ttempe/Pocket_Organ/3D models/V11 mock-up/Rendering with cover plate, flat surface.PNG

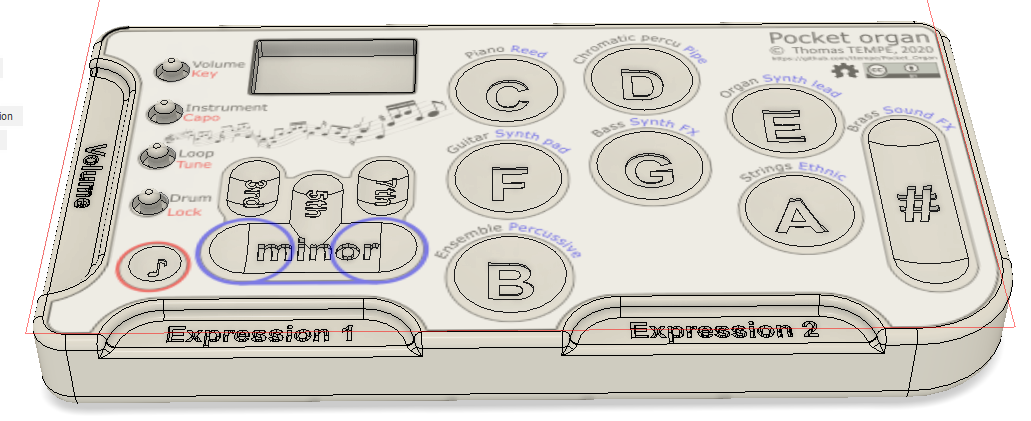
3D models/V11 mock-up/Rendering with cover plate, flat surface.PNG
