ttempe/Pocket_Organ/3D models/V11 mock-up/Rendering without cover plate.PNG

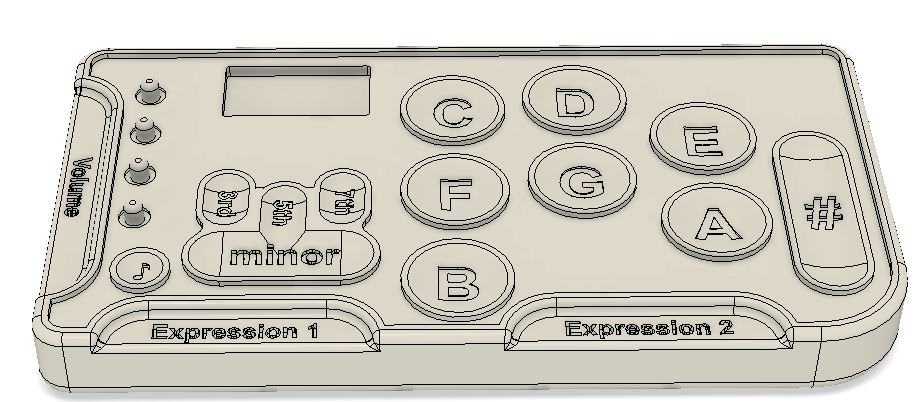
3D models/V11 mock-up/Rendering without cover plate.PNG
