ttempe/Pocket_Organ/Doc/2021-08-28 V19B/微信图片_20210825201405.jpg

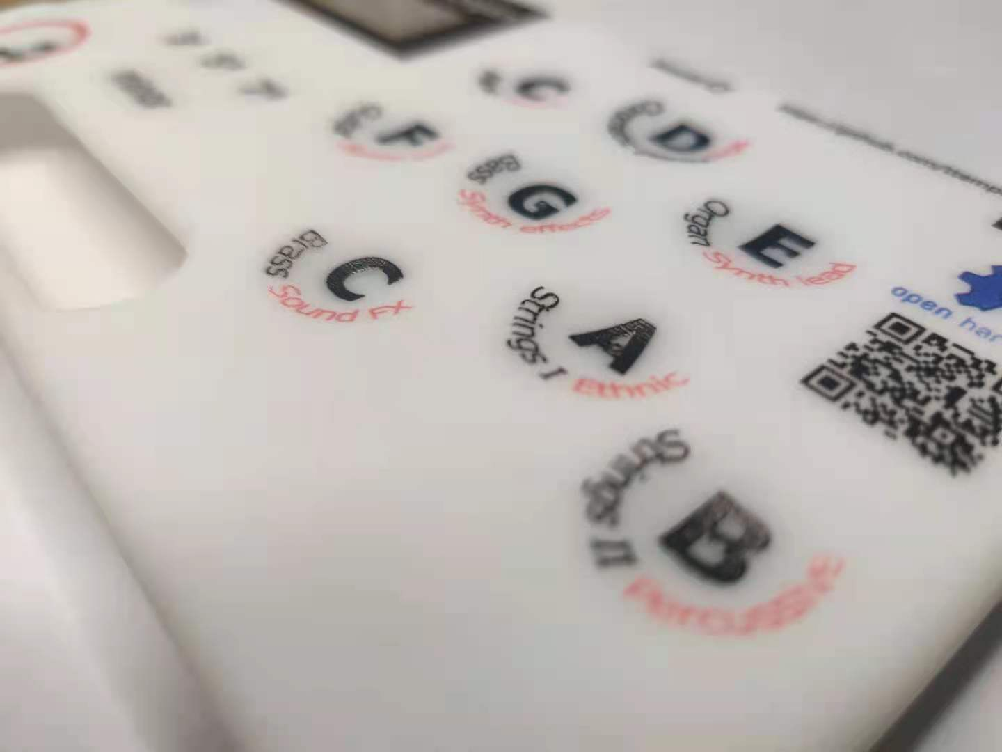
Doc/2021-08-28 V19B/微信图片_20210825201405.jpg
