ttempe/Pocket_Organ/Doc/2021-08-28 V19B/微信图片_20210828121017.jpg

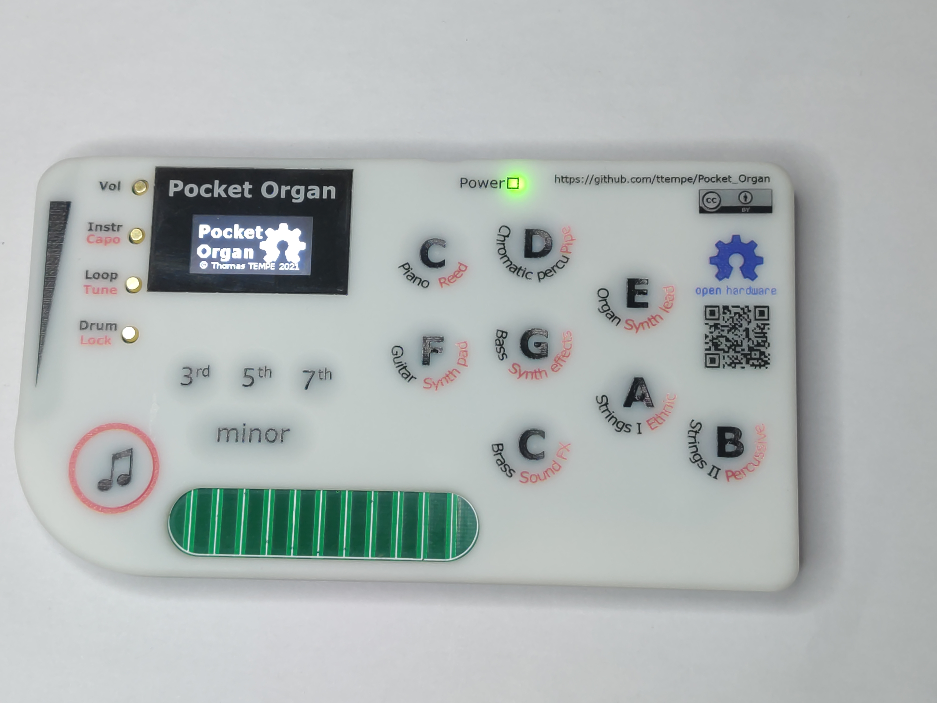
Doc/2021-08-28 V19B/微信图片_20210828121017.jpg
