ttempe/Pocket_Organ/Pictures/V3+/IMG_20180710_225816.jpg

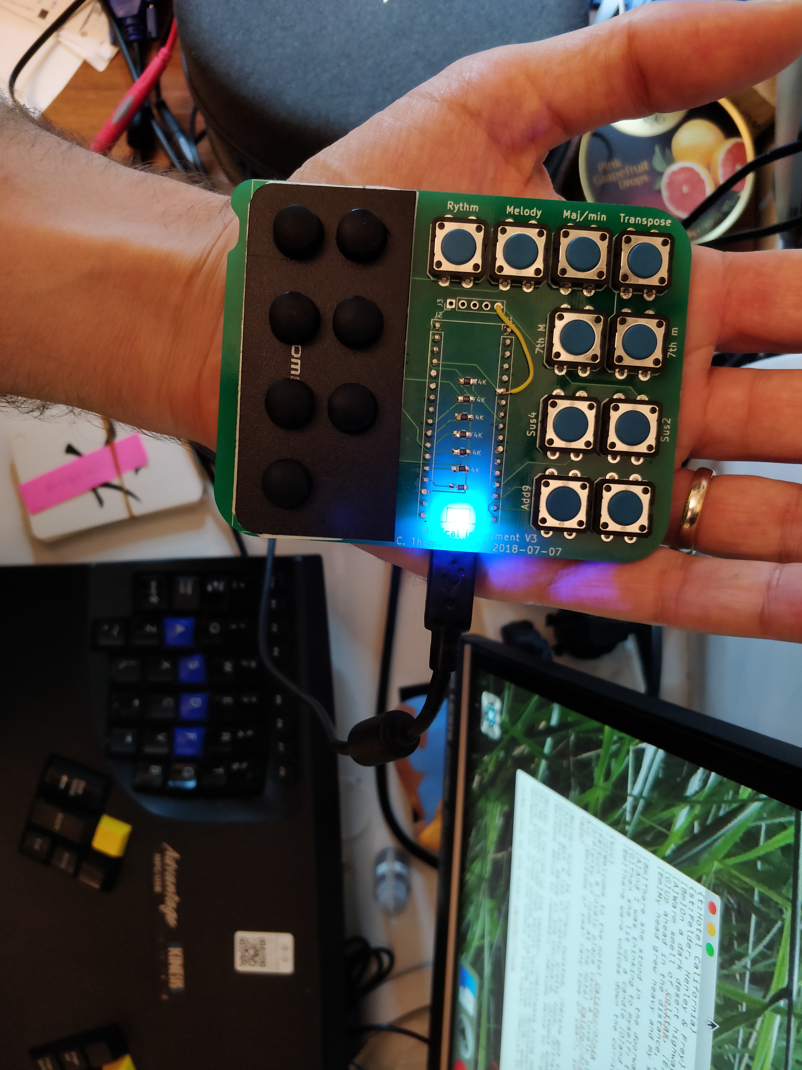
Pictures/V3+/IMG_20180710_225816.jpg
