ttempe/Pocket_Organ/Pictures/V3+/IMG_20190224_225914.jpg

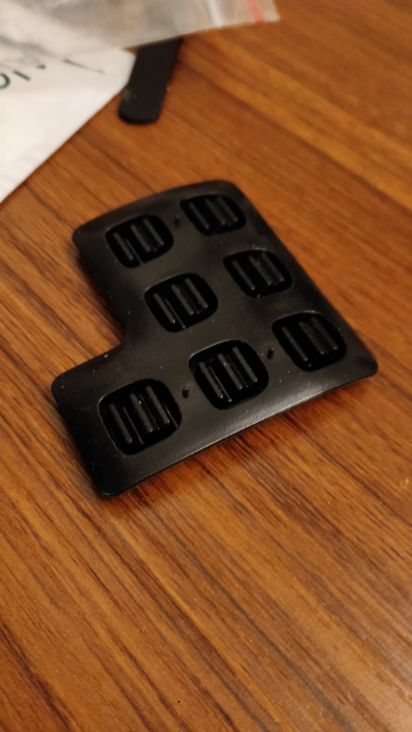
Pictures/V3+/IMG_20190224_225914.jpg
