ttempe/Pocket_Organ/Pictures/V3+/微信图片_20190317143241.jpg

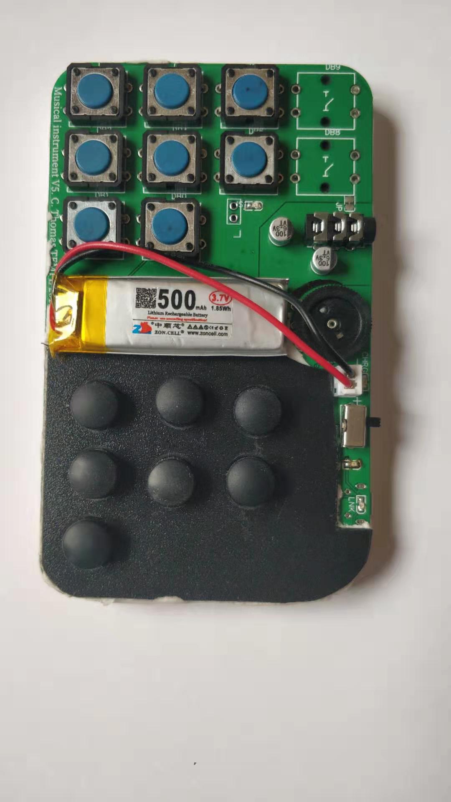
Pictures/V3+/微信图片_20190317143241.jpg
