ttempe/Pocket_Organ/Pictures/V3+/微信图片_20190317145705.jpg

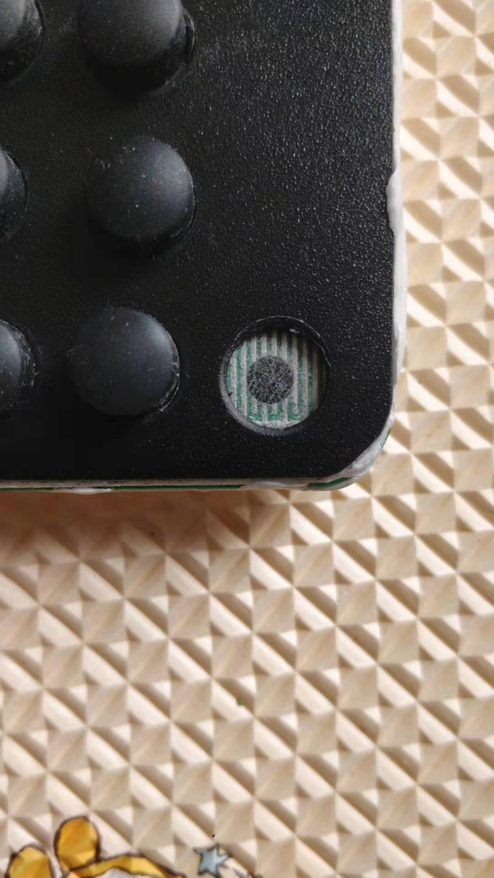
Pictures/V3+/微信图片_20190317145705.jpg
