ttempe/Pocket_Organ/3D models/V19/Pocket organ V19 for tool quote.step

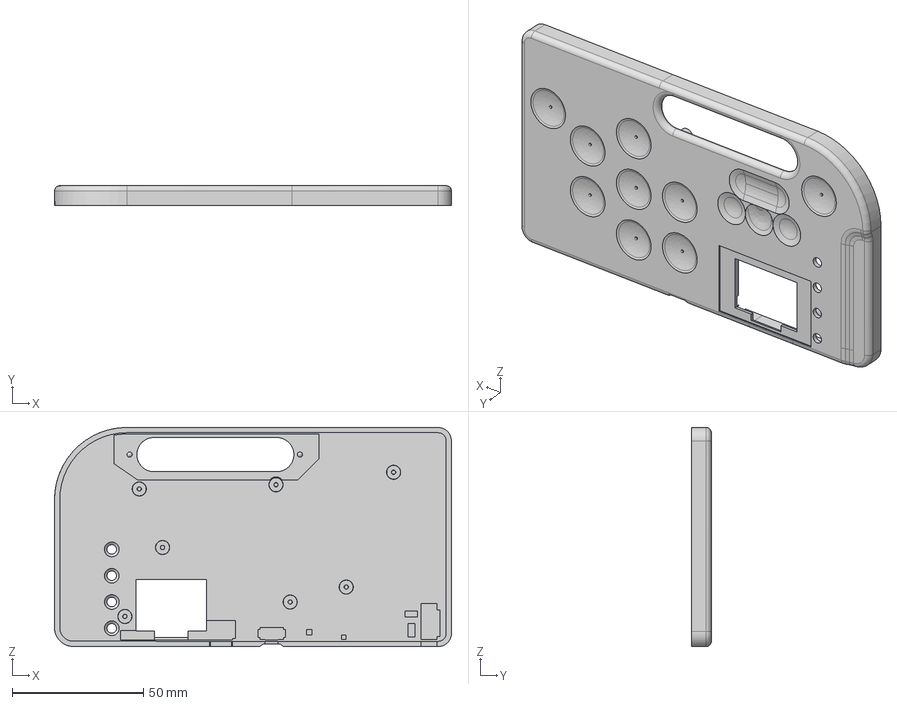
[picture p56: CAD file, 2021-10-30, an earlier design]
3D models/V19/Pocket organ V19 for tool quote.step
151.1 x 7.50 x 83.4 mm
