ttempe/Pocket_Organ/3D models/V11 prototype/top skin instructions.PNG

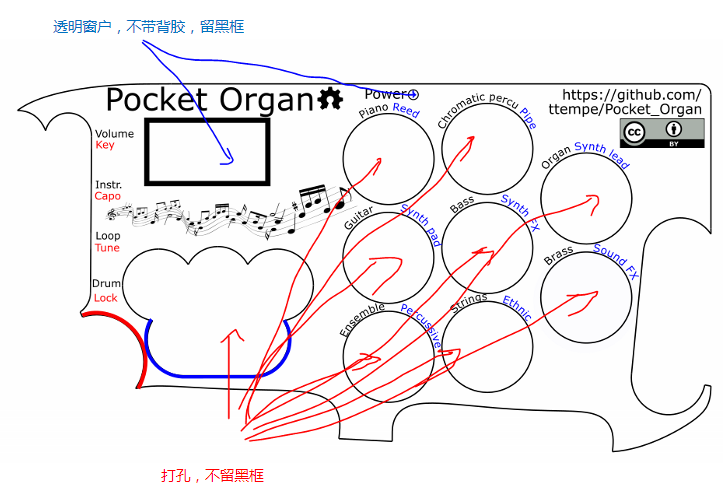
3D models/V11 prototype/top skin instructions.PNG
