ttempe/Pocket_Organ/Doc/2019-03-20 XCJ Music Makers open night poster .jpg

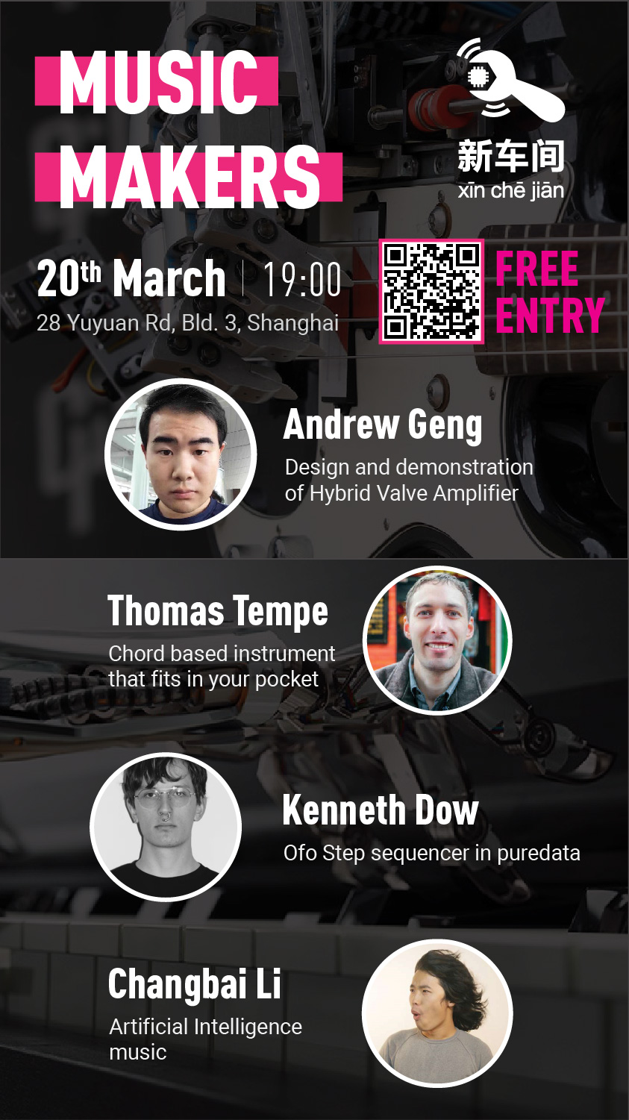
Doc/2019-03-20 XCJ Music Makers open night poster .jpg
