ttempe/Pocket_Organ/misc/2024-01-18 V23 hall effect sensor signal to noise measurements.xlsx

Sheet: 1x3mm magnet
34608
34640
34544
34656
34544
34608
34656
34656
34576
34688
34608
34624
34656
34688
34608
34608
34608
34656
34656
34720
34672
34640
34592
34640
34480
34624
34704
34688
34608
34624
34544
34688
34640
34656
34624
34656
34544
34592
34624
34704
34544
34720
34512
34608
34512
34656
34640
34640
34608
34720
34528
34544
34560
34656
34576
34688
34656
34640
34608
34640
34656
34592
34592
34640
34656
34624
34688
34624
34640
34720
34608
34688
34656
34624
34592
34640
34608
34624
34640
34640
34656
34640
34608
34720
34544
34592
34624
34624
34592
34624
34544
34640
34656
34624
34656
34640
34688
34576
34608
34640
34624
34640
34672
34720
34640
34656
34592
34592
34624
34624
34624
34688
34704
34688
34624
34592
34640
34528
34656
34768
34544
34640
34592
34704
34608
34720
34608
34624
34656
34688
34608
34720
34624
34512
34640
34640
34688
34720
34544
34608
34624
34624
34640
34640
34608
34640
34624
34688
34608
34656
34672
34608
34624
34640
34640
34656
34576
34624
34592
34656
34608
34688
34608
34576
34720
34640
34592
34576
34656
34640
34592
34688
34512
34608
34608
34624
34656
34640
34592
34640
34640
34640
34608
34656
34592
34624
34656
34496
34624
34656
34544
34608
34624
34640
34640
34624
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
