ttempe/Pocket_Organ/misc/V20 discharge curve - 2nd test.xlsx

timestamp | time | vbat | vusb | vbat_read16 | vusb_read16 | vref
7 | 00h00m07s | 4.433838 | 5.192986 | 43802 | 51452 | 65535
17 | 00h00m17s | 3.971279 | 2.644834 | 39417 | 26326 | 65535
27 | 00h00m27s | 3.955166 | 2.656113 | 39193 | 26262 | 65535
37 | 00h00m37s | 3.947109 | 2.630332 | 39561 | 26246 | 65535
48 | 00h00m48s | 3.972891 | 2.659336 | 39433 | 26038 | 65535
58 | 00h00m58s | 3.974502 | 2.657725 | 39209 | 26134 | 65535
68 | 00h01m08s | 3.947109 | 2.656113 | 38985 | 26182 | 65535
78 | 00h01m18s | 3.947109 | 2.646445 | 39449 | 26390 | 65535
88 | 00h01m28s | 3.951943 | 2.631943 | 39049 | 26358 | 65535
98 | 00h01m38s | 3.955166 | 2.646445 | 39113 | 26214 | 65535
109 | 00h01m49s | 3.916493 | 2.648057 | 39033 | 26326 | 65535
119 | 00h01m59s | 3.945498 | 2.631943 | 39177 | 26150 | 65535
129 | 00h02m09s | 3.932607 | 2.633554 | 39177 | 26374 | 65535
139 | 00h02m19s | 3.940664 | 2.654502 | 39193 | 26246 | 65535
149 | 00h02m29s | 3.939052 | 2.644834 | 39305 | 26134 | 65535
160 | 00h02m40s | 3.939052 | 2.654502 | 39113 | 26278 | 65535
170 | 00h02m50s | 3.94872 | 2.622275 | 39097 | 26310 | 65535
180 | 00h03m00s | 3.918105 | 2.644834 | 38905 | 26390 | 65535
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
