ttempe/Pocket_Organ/misc/V20 discharge curve - 1st test.xlsx

timestamp | time | vbat | vusb
205 | 00h03m25s | 4.427325 | 5.155847
215 | 00h03m35s | 4.422492 | 5.215466
225 | 00h03m45s | 4.422492 | 5.189685
236 | 00h03m56s | 3.964773 | 2.482049
246 | 00h04m06s | 3.945438 | 2.507831
256 | 00h04m16s | 3.926102 | 2.522333
266 | 00h04m26s | 3.945438 | 2.488495
276 | 00h04m36s | 3.932547 | 2.477216
286 | 00h04m46s | 3.921268 | 2.482049
296 | 00h04m56s | 3.916434 | 2.506219
307 | 00h05m07s | 3.934158 | 2.475604
317 | 00h05m17s | 3.914822 | 2.475604
327 | 00h05m27s | 3.909988 | 2.502997
337 | 00h05m37s | 3.926102 | 2.482049
347 | 00h05m47s | 3.932547 | 2.464224
357 | 00h05m57s | 3.913211 | 2.477216
368 | 00h06m08s | 3.889041 | 2.496552
378 | 00h06m18s | 3.932547 | 2.488495
388 | 00h06m28s | 3.921268 | 2.475604
398 | 00h06m38s | 3.893875 | 2.482049
408 | 00h06m48s | 3.86326 | 2.493329
418 | 00h06m58s | 3.895486 | 2.49494
429 | 00h07m09s | 3.908377 | 2.480438
439 | 00h07m19s | 3.880984 | 2.49494
449 | 00h07m29s | 3.932547 | 2.47067
459 | 00h07m39s | 3.90032 | 2.47067
469 | 00h07m49s | 3.918045 | 2.502997
479 | 00h07m59s | 3.87615 | 2.47067
490 | 00h08m10s | 3.932547 | 2.477216
500 | 00h08m20s | 3.880984 | 2.502997
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
