ttempe/Pocket_Organ/CircuitPy/polyphony.py

import array
import midi
import metronome
import board_po as board
import instr_names
from supervisor import ticks_ms
from keyboard import melody_bend_up, melody_bend_down

# Only one chord is ever sent at once.
# TODO:
# * Implement "#" button
# * Chords: When releasing a key, don't switch to the next one immediately, wait for a new keypress
# * add a "breath" key on chords, clean up the strumming code
# * when the note key is not pressed, turn off strumming notes as they are released
# * add modulation wheel expression (channel 1)
# * have Midi return the MIDI message string, and have Polyphony call the looper directly

scale = [60, 62, 64, 65, 67, 69, 71, 72]

LIVE_CHORD = 0
LIVE_MELODY = 1

def bits(n, nb=12):
    "bitmap iterator over set bits"
    for i in range(nb):
        if n & (1 << i):
            yield i

def round_note(n):
    return n%12 + 60

def on_bits(num):
    "iterate on bits that are set to 1"
    for i in range(8):
        if (num>>i)&1:
            yield i


class Polyphony:
    def __init__(self, keyboard, display, looper):
        self.pending = []   #list of notes scheduled for playing in the future
                            #format of each note: (note, velocity, ticks_ms)
        self.k = keyboard
        self.d = display
        self.l = looper
        self.midi = midi.Midi()
        self.metronome = metronome.Metronome(self.midi)
        self.transpose = 0
        self.melody_keys_transpose = array.array("b", [0]*8) #for keeping track of how which key was played
        self.instr = 22
        self.set_instr(self.instr)
        self.channel_volume = 100
        self.master_volume = 127 * 75 // 100
        self.set_channel_volume(self.channel_volume)
        self.set_master_volume(self.master_volume)
        self.global_tuning_tenths = 0
        self.set_global_tuning(0)
        self.chord = []        #Currently playing chord
        self.strumming = False #Enable strumming?
        self.strum_chord = []  #same chord, but with enough notes to cover all strumming keys
        self.strum_mute_old = False
        self.strum_keys_old = 0   #bitmap
        self.strum_keys_all = 0   #bitmap of all active notes
        self.default_velocity = 64
        
        #For continuous expression control
        self.playing_chord_key  = None #Number of the key being pressed, from 0 to 7
        self.playing_notes  = 0
        self.expr1_old      = self.default_velocity
        #self.expr1_time     = 0
        self.expr_bend_old  = 0
        #self.expr_bend_time = 0
        self.bend_baseline  = 0
        self.chord_shape_name = ""
        self.chord_sharp    = 0 #-1 for bemol, +1 for sharp
        self.chord_sharp_old= 0 #same; this value corresponds to the last one displayed
        self.chord_disp_timestamp = 0
        
        #For melody mode
        self.melody = False
        self.melody_last_key = None
        self.melody_last_key_time = 0
        self.melody_expr_bend_old = 0
        self.melody_expr_old = self.default_velocity
        
    def start_chord(self, quick_mode=False):
        self.playing_chord_key = self.k.current_note_key
        self.playing_chord_level = self.k.current_key_level
        self.root = round_note(self.k.current_key_level + self.transpose) #current_note_key should not be None

        #Determine the chord shape
        self.third = self.k.third
        self.sus4 = self.k.third and not self.k.minor
        self.sus2 = self.k.third and self.k.minor
        self.fifth = self.k.fifth
        self.aug = self.k.fifth and not self.k.minor
        self.dim = self.k.fifth and self.k.minor
        self.seventh = self.k.seventh
        self.minor = self.k.minor and not (self.dim or self.sus2)
        
        self.update_chord()

        if quick_mode:
            self.play_chord(self.default_velocity, 0)
        elif not self.k.strum_mute and not self.k.strum_keys:
            self.play_chord(self.default_velocity, 40)
        else:
            self.strum_keys_old = 0  # Play all held pads on the next loop()

    def update_chord(self):
        #Triad
        self.chord = [   round_note(self.root),                                             #The root
                         round_note(self.root + 4 - self.minor + self.sus4 - self.sus2*2),  #The 3rd
                         round_note(self.root + 7 + self.aug - self.dim)                    #The 5th
                         ]
        #Seventh
        if self.seventh:
            self.chord.append(round_note(self.root+10-self.minor))
        if 7 == self.playing_chord_key:
            #When playing Ut, Move the root key up one octave to make it sound different from Do
            self.chord[0]=self.chord[0]+12

        #Map the chord over the strumming keys
        unrounded_chord = [ self.root, self.root + 4 - self.minor + self.sus4 - self.sus2*2, self.root + 7 + self.aug - self.dim]
        if self.seventh:
            unrounded_chord.append(self.root+10-self.minor)
        self.stop_strumming()
        self.strum_chord = [unrounded_chord[0]-24]
        incr = -12
        while len(self.strum_chord) < board.STRUM_N_KEYS:
            for n in unrounded_chord:
                self.strum_chord.append(n+incr)
            incr += 12
                            
        #Prepare for display of chord name
        self.chord_shape_name =   ("m" if self.minor else "") + ("7" if self.seventh else "") + ("dim" if self.dim else "aug" if self.aug else "") + ("sus4" if self.sus4 else "sus2" if self.sus2 else "")
        self.chord_sharp_old = None #Force re-display next time
        #self.chord_disp_timestamp = 0 #Don't update -> display will be immediate on the next call to loop()
        self.strumming = True

    def play_chord(self, velocity, timing): #timing = number of ms between successive notes
        """Starts playing all notes for the chord.
        The 1st one is played immediately, the following ones are spaced by timing (in milliseconds).
        """
        self.l.append(self.midi.note_on(self.l.chord_channel, self.chord[0], velocity))
        for i, n in enumerate(self.chord[1:], start=1):
            if timing:
                self.pending.append((n, velocity, ticks_ms()+timing*i))
            else:
                self.l.append(self.midi.note_on(self.l.chord_channel, n, velocity))                
        
    def stop_chord(self):
        #self.l.append(self.midi.all_off(self.l.chord_channel))
        for n in self.chord:
            self.l.append(self.midi.note_off(self.l.chord_channel, n, self.default_velocity))
        # Mute sounding pads but keep last strum_chord so pads still play after release
        self._mute_strum_notes()
        self.strum_keys_old = 0  # re-trigger any pads still held
        self.pending = []
        self.d.clear()
        self.playing_chord_key = None
        self.expr1_none=-10
        self.chord_sharp_old = None
        
    def _mute_strum_notes(self):
        if self.strum_chord:
            for k in bits(self.strum_keys_all, board.STRUM_N_KEYS):
                self.l.append(self.midi.note_off(self.l.chord_channel, self.strum_chord[k], self.default_velocity))
            self.strum_keys_all = 0

    def stop_strumming(self):
        self._mute_strum_notes()
        self.strumming = False

    def start_note(self, i, sharp=False):
        #Third/Fifth/7th buttons are also used to play an octave up/down in melody mode. TODO: create specific variables in keyboard.py
        transpose = 12*self.k.fifth + 12*self.k.shift - 12*self.k.third + sharp #Move up or down based on the left-hand keys 
        self.melody_keys_transpose[i] = transpose
        self.l.append(self.midi.note_on(self.l.melody_channel, scale[i] + self.transpose + transpose, self.default_velocity))
    
    def stop_note(self, i):
        self.l.append(self.midi.note_off(self.l.melody_channel, scale[i] + self.transpose + self.melody_keys_transpose[i], self.default_velocity))

    def start_melody(self):
        self.melody = True
        self.melody_playing = 0 #bitmap of all playing notes
        self.melody_expr_bend_old = 0
        self.melody_expr_old = self.default_velocity
        self.l.append(self.midi.pitch_bend(self.l.melody_channel, 0))

    def stop_melody(self):
        self.melody = False
        self.melody_expr_bend_old = 0
        self.melody_expr_old = -10
        self.l.append(self.midi.pitch_bend(self.l.melody_channel, 0))
        self.l.append(self.midi.set_controller(self.l.melody_channel, 11, 127))

    def melody_note_names(self):
        "Pitch names of all keys currently sounding in melody mode, low to high."
        names = []
        for i in on_bits(self.melody_playing):
            midi = scale[i] + self.transpose + self.melody_keys_transpose[i]
            names.append((midi, instr_names.note_names[midi % 12]))
        names.sort()
        return tuple(n for _, n in names)

    def update_melody(self):
        for i in on_bits(self.k.bitmap ^ self.k.bitmap_old): #iterate over note key changes
            if (self.k.bitmap>>i)&1: #New keypress
                if self.melody_last_key !=None and abs(self.melody_last_key-i)==1 and (ticks_ms()-self.melody_last_key_time)<40 and min(self.melody_last_key, i) not in [2, 6]:
                    #two presses together; consider as a sharp.
                    self.stop_note(self.melody_last_key)
                    self.start_note(min(self.melody_last_key, i), sharp=True)
                    self.melody_playing &= ~(1<<self.melody_last_key) #un-record note
                    self.melody_playing |= 1<<min(self.melody_last_key, i) #record note
                    self.melody_last_key = None
                else: #Single note prhess
                    self.start_note(i, self.k.sharp)
                    self.melody_playing |= 1<<i #record note
                    self.melody_last_key = i
                    self.melody_last_key_time = ticks_ms()
            else: #Key release
                if (self.melody_playing>>i)&1: #was playing
                    self.stop_note(i)
                    self.melody_playing &= ~(1<<i) #un-record note
        expr_bend = (self.k.notes_val[melody_bend_up] - self.k.notes_val[melody_bend_down]) // 2
        if abs(expr_bend - self.melody_expr_bend_old) > 4:
            self.melody_expr_bend_old = expr_bend
            self.l.append(self.midi.pitch_bend(self.l.melody_channel, expr_bend))
        if self.k.current_note_key is not None:
            expr = self.k.notes_val[self.k.current_note_key]
            if abs(expr - self.melody_expr_old) > 10:
                self.melody_expr_old = expr
                self.l.append(self.midi.set_controller(self.l.melody_channel, 11, expr // 2 + 64))

    def stop_all_notes(self):
        self.playing_notes = 0
        self.l.append(self.midi.all_off(self.l.melody_channel))
        
    def play_drum(self, note):
        name, note = instr_names.drums[note]
        self.l.append(self.midi.note_on(self.l.drum_channel, note, self.default_velocity))
        return name

    def set_instr(self, instr):
        self.instr = instr
        self.midi.set_instr(self.l.chord_channel,  instr)
        self.midi.set_instr(self.l.melody_channel, instr)
        
    def set_channel_volume(self, vol):
        self.channel_volume = vol
        self.midi.set_controller(LIVE_CHORD, 7, vol)
        self.midi.set_controller(LIVE_MELODY, 7, vol)

    def bake_loop_channel_volume(self):
        "CC7 on loop channels for live monitoring while armed."
        for ch in (self.l.chord_channel, self.l.melody_channel):
            self.midi.set_controller(ch, 7, self.channel_volume)

    def prepend_loop_channel_volume(self):
        "CC7 baked into the loop at t=0 on first musical event."
        for ch in (self.l.chord_channel, self.l.melody_channel):
            msg = bytearray([0xB0 | (ch & 0x0F), 7, self.channel_volume & 0x7F])
            self.l.store.record_message(0, bytes(msg))
            self.l.record_lengths[self.l.recording] += 1

    def set_master_volume(self, vol):
        self.master_volume = vol
        self.midi.set_master_volume(vol)

    def set_global_tuning(self, tenths):
        self.global_tuning_tenths = max(-1000, min(1000, int(tenths)))
        self.midi.set_gs_master_tune(self.global_tuning_tenths)
        
    def loop(self):
        self.metronome.loop()
        
        #scheduled chord notes:
        #Check if a note is due for playing, and play it. Assumes the notes are listed chronologycally.
        if len(self.pending):
            next = self.pending[0][2]
            if next <= ticks_ms():
                n = self.pending.pop(0)
                self.l.append(self.midi.note_on(self.l.chord_channel, n[0], n[1]))

        # Strumming updates in chord, melody, and drum modes
        if self.strum_chord and self.strumming:
            # Mute-on-release when no chord key held (or explicit strum_mute)
            mute = self.k.strum_mute or (self.playing_chord_key is None)
            if mute and not self.strum_mute_old:
                #Just entered mute: silence pads that are not currently held
                for k in bits(self.strum_keys_all & ~self.k.strum_keys, board.STRUM_N_KEYS):
                    self.l.append(self.midi.note_off(self.l.chord_channel, self.strum_chord[k], self.default_velocity))
                self.strum_keys_all = self.k.strum_keys
            elif mute:
                #Keys that were in _old but are no longer in _new
                for i in bits(self.strum_keys_old & (~self.k.strum_keys), board.STRUM_N_KEYS):
                    self.l.append(self.midi.note_off(self.l.chord_channel, self.strum_chord[i], self.default_velocity))
                    self.strum_keys_all &= ~(1 << i)

            #update newly strummed keys
            for i in bits(self.k.strum_keys & (~self.strum_keys_old), board.STRUM_N_KEYS):
                self.l.append(self.midi.note_on(self.l.chord_channel, self.strum_chord[i], self.default_velocity))

            self.strum_mute_old = mute
            self.strum_keys_old = self.k.strum_keys
            self.strum_keys_all |= self.k.strum_keys

        if not self.melody: #Chord expression only outside melody play
            if self.playing_chord_key != None: #Playing a chord
                #Update sharp/flat status
                if self.playing_chord_level != self.k.current_key_level:
                    self.stop_chord()
                    self.start_chord()
                #Update chord shape
                if self.third != self.k.third:
                    self.l.append(self.midi.note_off(self.l.chord_channel, self.chord[1], self.default_velocity))
                    self.sus4 = self.k.third and not self.k.minor
                    self.sus2 = self.k.third and self.k.minor
                    self.third = self.k.third
                    self.update_chord()
                    self.l.append(self.midi.note_on(self.l.chord_channel, self.chord[1], self.default_velocity))
                if self.fifth != self.k.fifth:
                    self.l.append(self.midi.note_off(self.l.chord_channel, self.chord[2], self.default_velocity))
                    self.aug = self.k.fifth and not self.k.minor
                    self.dim = self.k.fifth and self.k.minor
                    self.fifth = self.k.fifth
                    self.update_chord()
                    self.l.append(self.midi.note_on(self.l.chord_channel, self.chord[2], self.default_velocity))
                if self.seventh and not self.k.seventh:
                    self.l.append(self.midi.note_off(self.l.chord_channel, self.chord[3], self.default_velocity))
                    self.seventh = self.k.seventh
                    self.update_chord()
                elif not self.seventh and self.k.seventh:
                    self.seventh = self.k.seventh
                    self.update_chord()
                    self.l.append(self.midi.note_on(self.l.chord_channel, self.chord[3], self.default_velocity))
                
                #Update expression
                #Channel expression (volume): vary pressure on the key being played
                expr1 = self.k.notes_val[self.playing_chord_key]
                if abs(expr1 - self.expr1_old) > 10:# and (ticks_ms() - self.expr1_time > 10):#Filtering
                    self.expr1_old = expr1
                    #self.expr1_time = ticks_ms()
                    self.l.append(self.midi.set_controller(self.l.chord_channel, 11, expr1//2+64))

                 #full-tone bending (press the 1st key of the previous/next line).
                expr_bend = (self.k.key_expr_up - self.k.key_expr_down)//2#+64            
                if abs(expr_bend - self.expr_bend_old) > 4:# and (ticks_ms() - self.expr_bend_time > 10):#Filtering
                    self.expr_bend_old = expr_bend
                    #self.expr_bend_time = ticks_ms()
                    self.l.append(self.midi.pitch_bend(self.l.chord_channel, expr_bend))


                #Update the display if needed (depends on the bending status)
                self.chord_sharp = 1 if expr_bend >28 else -1 if expr_bend <-27 else 0
                if self.chord_sharp != self.chord_sharp_old and (ticks_ms() - self.chord_disp_timestamp) > 200:
                    self.chord_sharp_old = self.chord_sharp
                    self.chord__disp_timestamp = ticks_ms()
                    #Don't count the "capo" in the chord display.
                    #Makes it harder to play with other musicians, but easier to follow tablatures
                    self.d.disp_chord(instr_names.note_names[(self.chord[0] + self.chord_sharp - self.transpose)%12], self.chord_shape_name) 
                                        
#end
