ttempe/Pocket_Organ/CircuitPy/instr_names.py

instrument_families = [
    "Piano",
    "Chromatic percussion",
    "Organ",
    "Guitar",
    "Bass",
    "Strings I",
    "Strings II",
    "Brass",
    "Reed",
    "Pipe",
    "Synth lead",
    "Synth pad",
    "Synth effects",
    "Ethnic",
    "Percussive",
    "Sound effects"
    ]

instrument_names = [
    "Acoustic Grand Piano",
    "Bright Acoustic Piano",
    "Electric Grand Piano",
    "Honky-tonk Piano",
    "Electric Piano 1",
    "Electric Piano 2",
    "Harpsichord",
    "Clavinet",
    "Celesta",
    "Glockenspiel",
    "Music Box",
    "Vibraphone",
    "Marimba",
    "Xylophone",
    "Tubular Bells",
    "Dulcimer",
    "Drawbar Organ",
    "Percussive Organ",
    "Rock Organ",
    "Church Organ",
    "Reed Organ",
    "Accordion",
    "Harmonica",
    "Tango Accordion",
    "Acoustic Guitar (nylon)",
    "Acoustic Guitar (steel)",
    "Electric Guitar (jazz)",
    "Electric Guitar (clean)",
    "Electric Guitar (muted)",
    "Overdriven Guitar",
    "Distortion Guitar",
    "Guitar harmonics",
    "Acoustic Bass",
    "Electric Bass (finger)",
    "Electric Bass (pick)",
    "Fretless Bass",
    "Slap Bass 1",
    "Slap Bass 2",
    "Synth Bass 1",
    "Synth Bass 2",
    "Violin",
    "Viola",
    "Cello",
    "Contrabass",
    "Tremolo Strings",
    "Pizzicato Strings",
    "Orchestral Harp",
    "Timpani",
    "String Ensemble 1",
    "String Ensemble 2",
    "Synth Strings 1",
    "Synth Strings 2",
    "Choir Aahs",
    "Voice Oohs",
    "Synth Voice",
    "Orchestra Hit",
    "Trumpet",
    "Trombone",
    "Tuba",
    "Muted Trumpet",
    "French Horn",
    "Brass Section",
    "Synth Brass 1",
    "Synth Brass 2",
    "Soprano Sax",
    "Alto Sax",
    "Tenor Sax",
    "Baritone Sax",
    "Oboe",
    "English Horn",
    "Bassoon",
    "Clarinet",
    "Piccolo",
    "Flute",
    "Recorder",
    "Pan Flute",
    "Blown Bottle",
    "Shakuhachi",
    "Whistle",
    "Ocarina",
    "Lead 1 (square)",
    "Lead 2 (sawtooth)",
    "Lead 3 (calliope)",
    "Lead 4 (chiff)",
    "Lead 5 (charang)",
    "Lead 6 (voice)",
    "Lead 7 (fifths)",
    "Lead 8 (bass + lead)",
    "Pad 1 (new age)",
    "Pad 2 (warm)",
    "Pad 3 (polysynth)",
    "Pad 4 (choir)",
    "Pad 5 (bowed)",
    "Pad 6 (metallic)",
    "Pad 7 (halo)",
    "Pad 8 (sweep)",
    "FX 1 (rain)",
    "FX 2 (soundtrack)",
    "FX 3 (crystal)",
    "FX 4 (atmosphere)",
    "FX 5 (brightness)",
    "FX 6 (goblins)",
    "FX 7 (echoes)",
    "FX 8 (sci-fi)",
    "Sitar",
    "Banjo",
    "Shamisen",
    "Koto",
    "Kalimba",
    "Bag pipe",
    "Fiddle",
    "Shanai",
    "Tinkle Bell",
    "Agogo",
    "Steel Drums",
    "Woodblock",
    "Taiko Drum",
    "Melodic Tom",
    "Synth Drum",
    "Reverse Cymbal",
    "Guitar Fret Noise",
    "Breath Noise",
    "Seashore",
    "Bird Tweet",
    "Telephone Ring",
    "Helicopter",
    "Applause",
    "Gunshot"
    ]

note_names = ["C", "C#", "D", "D#", "E", "F", "F#", "G", "G#", "A", "A#", "B", "C"]

drums = [("Snare", 38), ("Bass drum", 36), ("Ride cymbal", 51), ("Low tom", 45), ("Mid tom", 48), ("High tom", 50), ("Open hi-hat", 46), ("Closed hi-hat", 42), ("Crash cymbal", 49) ]

#End
